gexwing/AVR_LedStripes/LTSpice/polarityprotection_nchannel.asc

M2: nmos; Si7102DN
R1: res; 10k
V1: voltage; PULSE(-2 2 1 1e-2 1e-2 .1 .2)
Named nets: 0
.tran 5
