gexwing/AVR_LedStripes/LTSpice/preamp_opamp2.asc

C1: cap; 4µ7
R1: res; 10k
R2: res; 10k
R3: res; 50k
R4: res; 1k
U1: LTC6242
V1: voltage; SINE(5 .1 400); AC .1
V2: voltage; 5
Named nets: 0, +5V
.ac dec 10 10 100k
;tran .1
Maybe tunable via pot
