gexwing/AVR_LedStripes/LTSpice/Lowpass.asc

C1: cap; 4µ7
R1: res; {R}
V1: voltage; AC 1
Named nets: 0
.ac dec 20 1 50k
.step param R 10k 100k 5k
