gexwing/AVR_LedStripes/LTSpice/preamp_opamp.asc

C2: cap; 4n7
R1: res; 10k
R2: res; 10k
R3: res; 1k
R4: res; 10k
R5: res; 12k
U1: LT1001
V1: voltage; 5
V2: voltage; SINE(0 .05 800)
Named nets: +5V, 0
.tran .2
