gexwing/AVR_LedStripes/LTSpice/polarityprotection_pchannel.asc

M1: pmos; FDS4953
R1: res; 10k
V1: voltage; PULSE(-12 12 2 0)
Named nets: 0
.tran 5
